cfoge/Video_EQ/lazercut_case/IMG_9145.jpeg

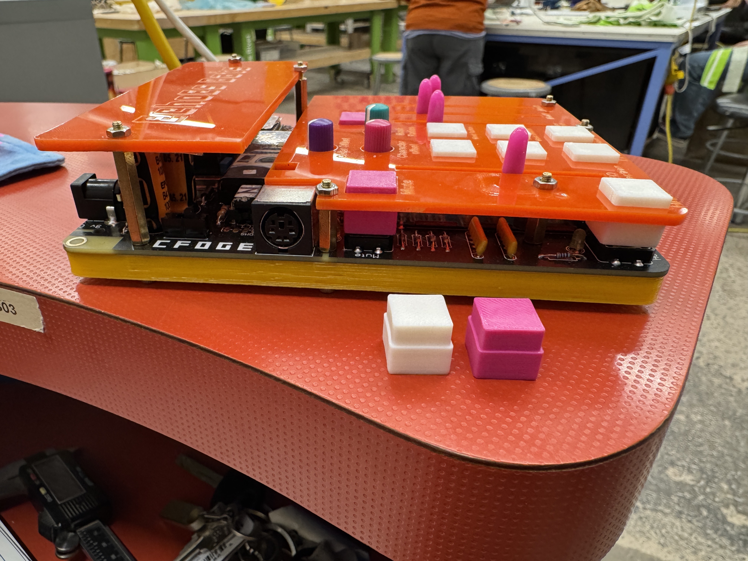
lazercut_case/IMG_9145.jpeg
