cfoge/Video_EQ/lazercut_case/IMG_9146.jpeg

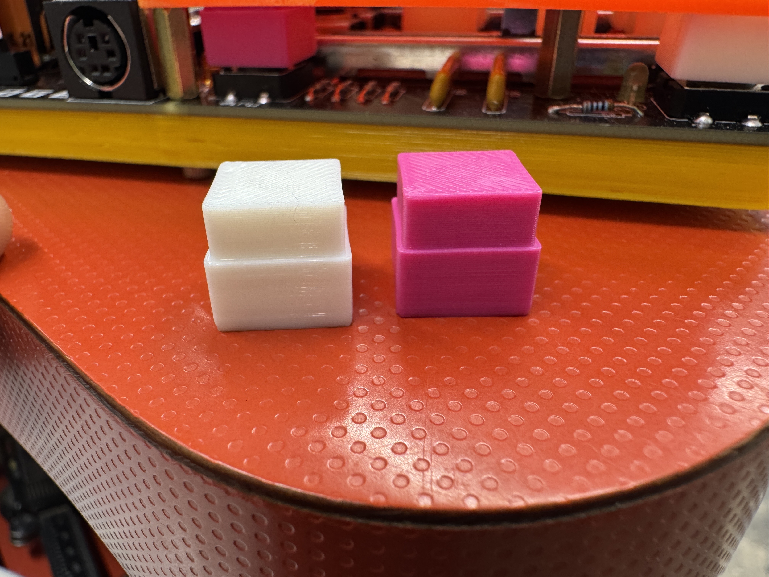
lazercut_case/IMG_9146.jpeg
