cfoge/Video_EQ/lazercut_case/IMG_9147.jpeg

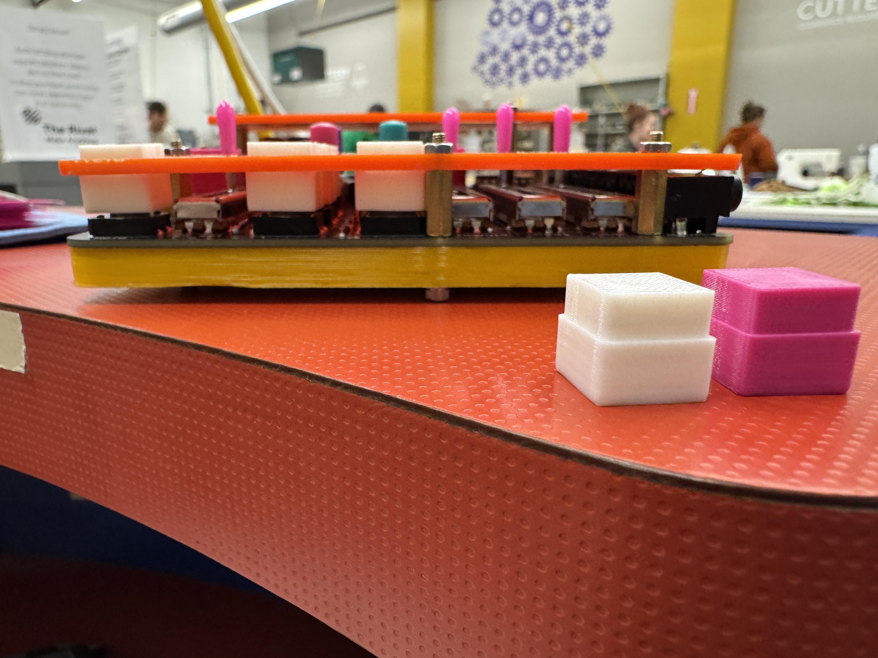
lazercut_case/IMG_9147.jpeg
