cfoge/Video_EQ/lazercut_case/IMG_9148.jpeg

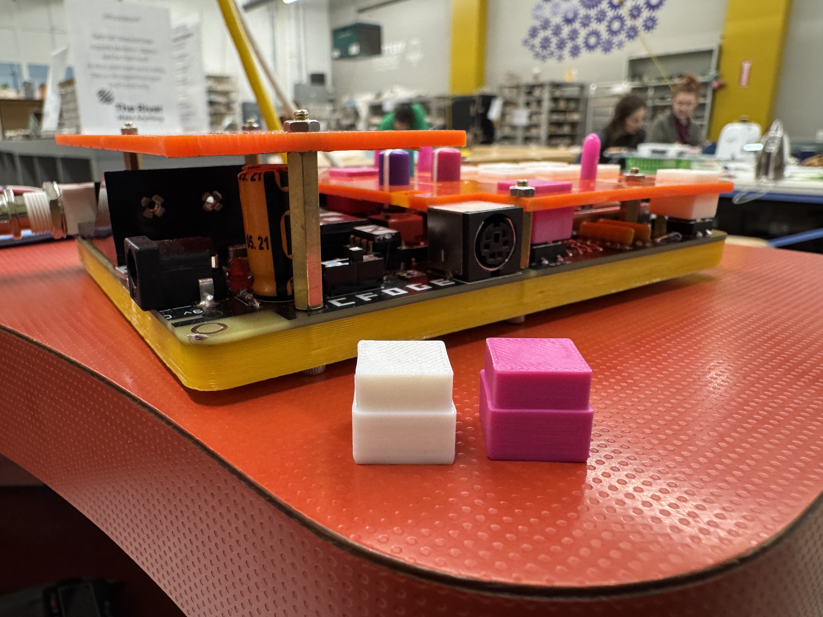
lazercut_case/IMG_9148.jpeg
